techie66/EngineDataLogger-FrontControls/firmware/imu/MPU6050_imu.h

// I2Cdev and MPU6050 must be installed as libraries, or else the .cpp/.h files
// for both classes must be in the include path of your project
#include "I2Cdev.h"

#include "MPU6050_6Axis_MotionApps612.h"
//#include "MPU6050.h" // not necessary if using MotionApps include file

// Arduino Wire library is required if I2Cdev I2CDEV_ARDUINO_WIRE implementation
// is used in I2Cdev.h
#if I2CDEV_IMPLEMENTATION == I2CDEV_ARDUINO_WIRE
#include "Wire.h"
#endif

// class default I2C address is 0x68
// specific I2C addresses may be passed as a parameter here
// AD0 low = 0x68 (default for SparkFun breakout and InvenSense evaluation board)
// AD0 high = 0x69
//MPU6050 mpu;
MPU6050 mpu(0x69); // <-- use for AD0 high

/* =========================================================================
   NOTE: In addition to connection 3.3v, GND, SDA, and SCL, this sketch
   depends on the MPU-6050's INT pin being connected to the Arduino's
   external interrupt #0 pin. On the Arduino Uno and Mega 2560, this is
   digital I/O pin 2.
   ========================================================================= */

/* =========================================================================
   NOTE: Arduino v1.0.1 with the Leonardo board generates a compile error
   when using Serial.write(buf, len). The Teapot output uses this method.
   The solution requires a modification to the Arduino USBAPI.h file, which
   is fortunately simple, but annoying. This will be fixed in the next IDE
   release. For more info, see these links:

   http://arduino.cc/forum/index.php/topic,109987.0.html
   http://code.google.com/p/arduino/issues/detail?id=958
   ========================================================================= */



// uncomment "OUTPUT_READABLE_QUATERNION" if you want to see the actual
// quaternion components in a [w, x, y, z] format (not best for parsing
// on a remote host such as Processing or something though)
//#define OUTPUT_READABLE_QUATERNION

// uncomment "OUTPUT_READABLE_EULER" if you want to see Euler angles
// (in degrees) calculated from the quaternions coming from the FIFO.
// Note that Euler angles suffer from gimbal lock (for more info, see
// http://en.wikipedia.org/wiki/Gimbal_lock)
//#define OUTPUT_READABLE_EULER

// uncomment "OUTPUT_READABLE_YAWPITCHROLL" if you want to see the yaw/
// pitch/roll angles (in degrees) calculated from the quaternions coming
// from the FIFO. Note this also requires gravity vector calculations.
// Also note that yaw/pitch/roll angles suffer from gimbal lock (for
// more info, see: http://en.wikipedia.org/wiki/Gimbal_lock)
#define OUTPUT_READABLE_YAWPITCHROLL

// uncomment "OUTPUT_READABLE_REALACCEL" if you want to see acceleration
// components with gravity removed. This acceleration reference frame is
// not compensated for orientation, so +X is always +X according to the
// sensor, just without the effects of gravity. If you want acceleration
// compensated for orientation, us OUTPUT_READABLE_WORLDACCEL instead.
//#define OUTPUT_READABLE_REALACCEL

// uncomment "OUTPUT_READABLE_WORLDACCEL" if you want to see acceleration
// components with gravity removed and adjusted for the world frame of
// reference (yaw is relative to initial orientation, since no magnetometer
// is present in this case). Could be quite handy in some cases.
//#define OUTPUT_READABLE_WORLDACCEL

// uncomment "OUTPUT_TEAPOT" if you want output that matches the
// format used for the InvenSense teapot demo
//#define OUTPUT_TEAPOT



#define INTERRUPT_PIN 3  // use pin 2 on Arduino Uno & most boards
#define LED_PIN 13 // (Arduino is 13, Teensy is 11, Teensy++ is 6)
bool blinkState = false;

// MPU control/status vars
bool dmpReady = false;  // set true if DMP init was successful
uint8_t mpuIntStatus;   // holds actual interrupt status byte from MPU
uint8_t devStatus;      // return status after each device operation (0 = success, !0 = error)
uint16_t packetSize;    // expected DMP packet size (default is 42 bytes)
uint16_t fifoCount;     // count of all bytes currently in FIFO
uint8_t fifoBuffer[64]; // FIFO storage buffer

// orientation/motion vars
Quaternion q;           // [w, x, y, z]         quaternion container
VectorInt16 aa;         // [x, y, z]            accel sensor measurements
VectorInt16 gy;         // [x, y, z]            gyro sensor measurements
VectorInt16 aaReal;     // [x, y, z]            gravity-free accel sensor measurements
VectorInt16 aaWorld;    // [x, y, z]            world-frame accel sensor measurements
VectorFloat gravity;    // [x, y, z]            gravity vector
float euler[3];         // [psi, theta, phi]    Euler angle container
float ypr[3];           // [yaw, pitch, roll]   yaw/pitch/roll container and gravity vector

// packet structure for InvenSense teapot demo
uint8_t teapotPacket[14] = { '$', 0x02, 0, 0, 0, 0, 0, 0, 0, 0, 0x00, 0x00, '\r', '\n' };

void MPU_setup()
{
  // NOTE: 8MHz or slower host processors, like the Teensy @ 3.3V or Arduino
  // Pro Mini running at 3.3V, cannot handle this baud rate reliably due to
  // the baud timing being too misaligned with processor ticks. You must use
  // 38400 or slower in these cases, or use some kind of external separate
  // crystal solution for the UART timer.

  // initialize device
  Serial.println(F("Initializing I2C devices..."));
  mpu.initialize();
  pinMode(INTERRUPT_PIN, INPUT);

  // verify connection
  Serial.println(F("Testing device connections..."));
  Serial.println(mpu.testConnection() ? F("MPU6050 connection successful") : F("MPU6050 connection failed"));
  mpu.setFullScaleAccelRange(0); // 0 = +-2g

  // wait for ready
  /* Don't
  Serial.println(F("\nSend any character to begin DMP programming and demo: "));
  while (Serial.available() && Serial.read()); // empty buffer
  while (!Serial.available());                 // wait for data
  while (Serial.available() && Serial.read()); // empty buffer again
  */

  // load and configure the DMP
  Serial.println(F("Initializing DMP..."));
  devStatus = mpu.dmpInitialize();

  // supply your own gyro offsets here, scaled for min sensitivity
  mpu.setXGyroOffset(-95);
  mpu.setYGyroOffset(29);
  mpu.setZGyroOffset(57);
  mpu.setXAccelOffset(-1248);
  mpu.setYAccelOffset(827);
  mpu.setZAccelOffset(1509);
  // make sure it worked (returns 0 if so)
  if (devStatus == 0) {
    // Calibration Time: generate offsets and calibrate our MPU6050
    //mpu.CalibrateAccel(6);
    //mpu.CalibrateGyro(6);
    Serial.println();
    mpu.PrintActiveOffsets();
    // turn on the DMP, now that it's ready
    Serial.println(F("Enabling DMP..."));
    mpu.setDMPEnabled(true);

    // enable Arduino interrupt detection
    Serial.print(F("Enabling interrupt detection (Arduino external interrupt "));
    Serial.print(digitalPinToInterrupt(INTERRUPT_PIN));
    Serial.println(F(")..."));
    mpuIntStatus = mpu.getIntStatus();

    // set our DMP Ready flag so the main loop() function knows it's okay to use it
    Serial.println(F("DMP ready! Waiting for first interrupt..."));
    dmpReady = true;

    // get expected DMP packet size for later comparison
    packetSize = mpu.dmpGetFIFOPacketSize();
  } else {
    // ERROR!
    // 1 = initial memory load failed
    // 2 = DMP configuration updates failed
    // (if it's going to break, usually the code will be 1)
    Serial.print(F("DMP Initialization failed (code "));
    Serial.print(devStatus);
    Serial.println(F(")"));
  }

  // configure LED for output
  pinMode(LED_PIN, OUTPUT);
}

void MPU_loop()
{
  // if programming failed, don't try to do anything
  if (!dmpReady) return;
  // read a packet from FIFO
  if (mpu.dmpGetCurrentFIFOPacket(fifoBuffer)) { // Get the Latest packet 

#ifdef OUTPUT_READABLE_QUATERNION
    // display quaternion values in easy matrix form: w x y z
    mpu.dmpGetQuaternion(&q, fifoBuffer);
    Serial.print("quat\t");
    Serial.print(q.w);
    Serial.print("\t");
    Serial.print(q.x);
    Serial.print("\t");
    Serial.print(q.y);
    Serial.print("\t");
    Serial.println(q.z);
#endif

#ifdef OUTPUT_READABLE_EULER
    // display Euler angles in degrees
    mpu.dmpGetQuaternion(&q, fifoBuffer);
    mpu.dmpGetEuler(euler, &q);
    Serial.print("euler\t");
    Serial.print(euler[0] * 180 / M_PI);
    Serial.print("\t");
    Serial.print(euler[1] * 180 / M_PI);
    Serial.print("\t");
    Serial.println(euler[2] * 180 / M_PI);
#endif

#ifdef OUTPUT_READABLE_YAWPITCHROLL
    // display Euler angles in degrees
    mpu.dmpGetQuaternion(&q, fifoBuffer);
    mpu.dmpGetGravity(&gravity, &q);
    mpu.dmpGetYawPitchRoll(ypr, &q, &gravity);
    //Serial.print("ypr\t");
    Serial.print("r\t");
    //Serial.print(ypr[0] * 180 / M_PI);
    //Serial.print("\t");
    //Serial.print(ypr[1] * 180 / M_PI);
    //Serial.print("\t");
    Serial.print(ypr[2] * 180 / M_PI);
    /*
      mpu.dmpGetAccel(&aa, fifoBuffer);
      Serial.print("\tRaw Accl XYZ\t");
      Serial.print(aa.x);
      Serial.print("\t");
      Serial.print(aa.y);
      Serial.print("\t");
      Serial.print(aa.z);
      mpu.dmpGetGyro(&gy, fifoBuffer);
      Serial.print("\tRaw Gyro XYZ\t");
      Serial.print(gy.x);
      Serial.print("\t");
      Serial.print(gy.y);
      Serial.print("\t");
      Serial.print(gy.z);
    */
    Serial.println();

#endif

#ifdef OUTPUT_READABLE_REALACCEL
    // display real acceleration, adjusted to remove gravity
    mpu.dmpGetQuaternion(&q, fifoBuffer);
    mpu.dmpGetAccel(&aa, fifoBuffer);
    mpu.dmpGetGravity(&gravity, &q);
    mpu.dmpGetLinearAccel(&aaReal, &aa, &gravity);
    Serial.print("areal\t");
    Serial.print(aaReal.x);
    Serial.print("\t");
    Serial.print(aaReal.y);
    Serial.print("\t");
    Serial.println(aaReal.z);
#endif

#ifdef OUTPUT_READABLE_WORLDACCEL
    // display initial world-frame acceleration, adjusted to remove gravity
    // and rotated based on known orientation from quaternion
    mpu.dmpGetQuaternion(&q, fifoBuffer);
    mpu.dmpGetAccel(&aa, fifoBuffer);
    mpu.dmpGetGravity(&gravity, &q);
    mpu.dmpGetLinearAccel(&aaReal, &aa, &gravity);
    mpu.dmpGetLinearAccelInWorld(&aaWorld, &aaReal, &q);
    Serial.print("aworld\t");
    Serial.print(aaWorld.x);
    Serial.print("\t");
    Serial.print(aaWorld.y);
    Serial.print("\t");
    Serial.println(aaWorld.z);
#endif

#ifdef OUTPUT_TEAPOT
    // display quaternion values in InvenSense Teapot demo format:
    teapotPacket[2] = fifoBuffer[0];
    teapotPacket[3] = fifoBuffer[1];
    teapotPacket[4] = fifoBuffer[4];
    teapotPacket[5] = fifoBuffer[5];
    teapotPacket[6] = fifoBuffer[8];
    teapotPacket[7] = fifoBuffer[9];
    teapotPacket[8] = fifoBuffer[12];
    teapotPacket[9] = fifoBuffer[13];
    Serial.write(teapotPacket, 14);
    teapotPacket[11]++; // packetCount, loops at 0xFF on purpose
#endif

    // blink LED to indicate activity
    blinkState = !blinkState;
    digitalWrite(LED_PIN, blinkState);

  }
}


uint16_t MPU_loop2()
{
  // if programming failed, don't try to do anything
  if (!dmpReady) return 3602;
  // read a packet from FIFO
  if (mpu.dmpGetCurrentFIFOPacket(fifoBuffer)) { // Get the Latest packet 

    // display Euler angles in degrees
    mpu.dmpGetQuaternion(&q, fifoBuffer);
    mpu.dmpGetGravity(&gravity, &q);
    mpu.dmpGetYawPitchRoll(ypr, &q, &gravity);
    uint16_t roll_CAN = ( (ypr[2] * 180 / M_PI) + 180 ) * 10;
    // blink LED to indicate activity
    blinkState = !blinkState;
    digitalWrite(LED_PIN, blinkState);
    return roll_CAN;
    //return 1800;
    /*Serial.print("ypr\t");
    Serial.print(ypr[0] * 180 / M_PI);
    Serial.print("\t");
    Serial.print(ypr[1] * 180 / M_PI);
    Serial.print("\t");
    Serial.print(ypr[2] * 180 / M_PI);

      mpu.dmpGetAccel(&aa, fifoBuffer);
      Serial.print("\tRaw Accl XYZ\t");
      Serial.print(aa.x);
      Serial.print("\t");
      Serial.print(aa.y);
      Serial.print("\t");
      Serial.print(aa.z);
      mpu.dmpGetGyro(&gy, fifoBuffer);
      Serial.print("\tRaw Gyro XYZ\t");
      Serial.print(gy.x);
      Serial.print("\t");
      Serial.print(gy.y);
      Serial.print("\t");
      Serial.print(gy.z);

    Serial.println();
    */


#ifdef OUTPUT_READABLE_REALACCEL
    // display real acceleration, adjusted to remove gravity
    mpu.dmpGetQuaternion(&q, fifoBuffer);
    mpu.dmpGetAccel(&aa, fifoBuffer);
    mpu.dmpGetGravity(&gravity, &q);
    mpu.dmpGetLinearAccel(&aaReal, &aa, &gravity);
/*
    Serial.print("areal\t");
    Serial.print(aaReal.x);
    Serial.print("\t");
    Serial.print(aaReal.y);
    Serial.print("\t");
    Serial.println(aaReal.z);
*/
#endif


  }
  return 3601;
}
